microsoft/DMXInspector/Case/pics/FullCase.jpg

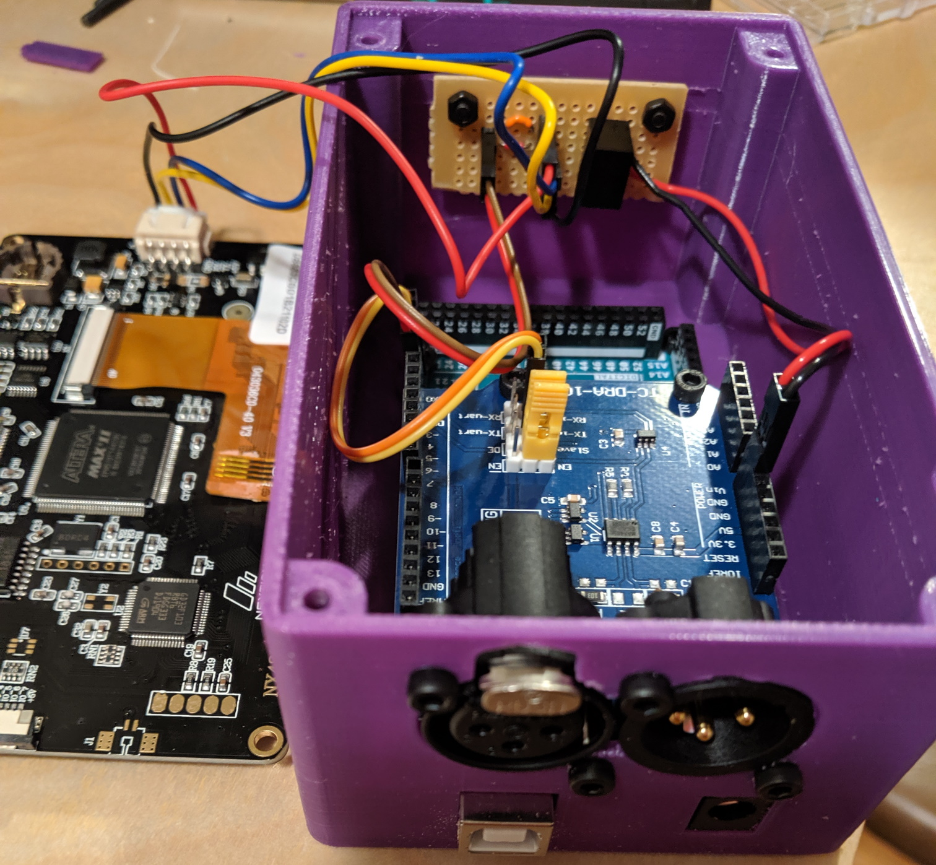
Case/pics/FullCase.jpg
